RBinsonB/sharkhead-tx2-case/documentation/pictures/buttons_cad.png

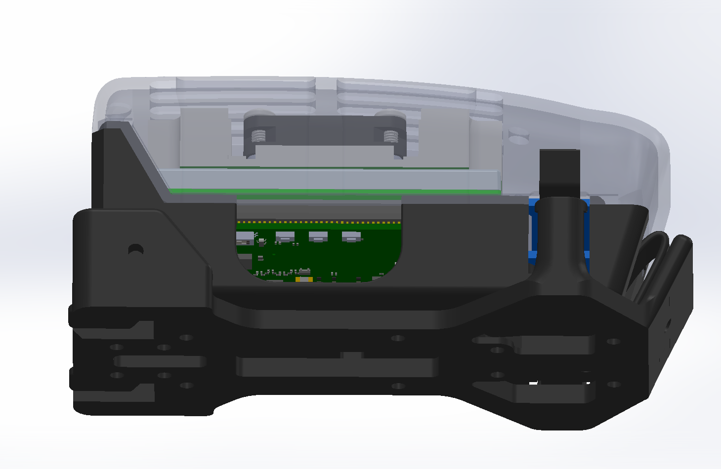
documentation/pictures/buttons_cad.png
