RBinsonB/sharkhead-tx2-case/documentation/pictures/gpio_cad.png

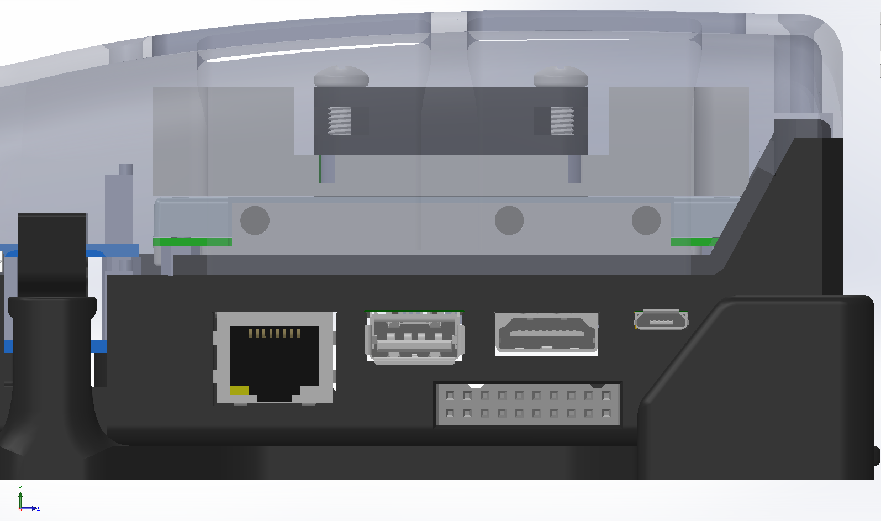
documentation/pictures/gpio_cad.png
