RBinsonB/sharkhead-tx2-case/documentation/pictures/gpio_cad_details.png

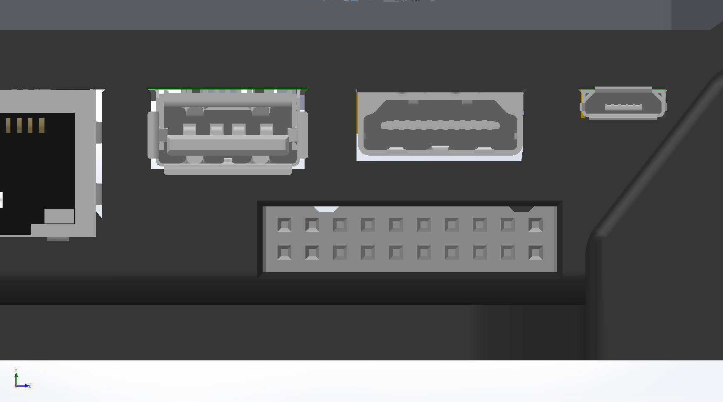
documentation/pictures/gpio_cad_details.png
