RBinsonB/sharkhead-tx2-case/documentation/pictures/rear_cad.png

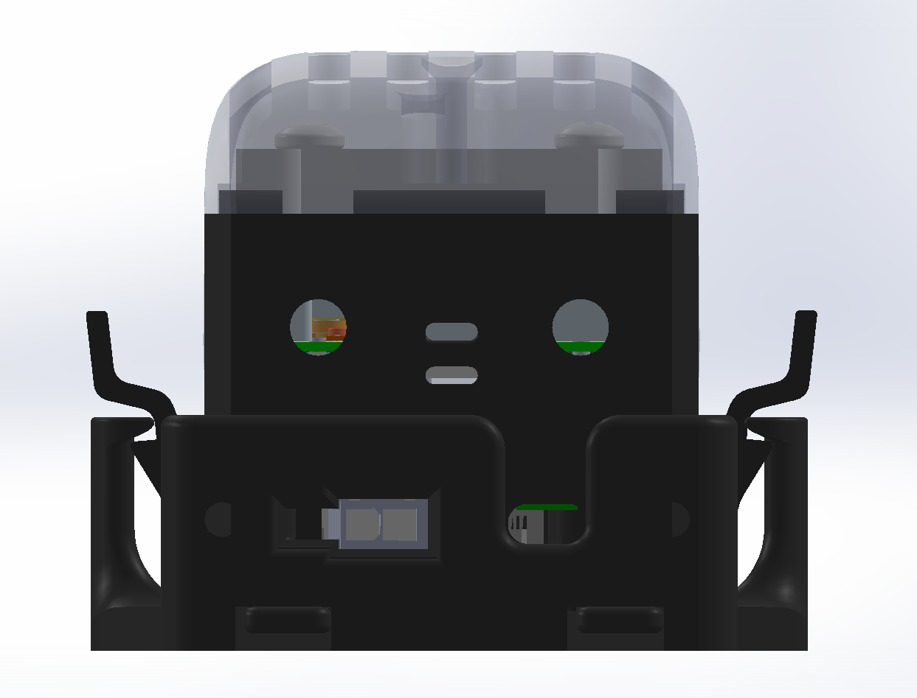
documentation/pictures/rear_cad.png
