RBinsonB/sharkhead-tx2-case/documentation/pictures/removing_1.jpg

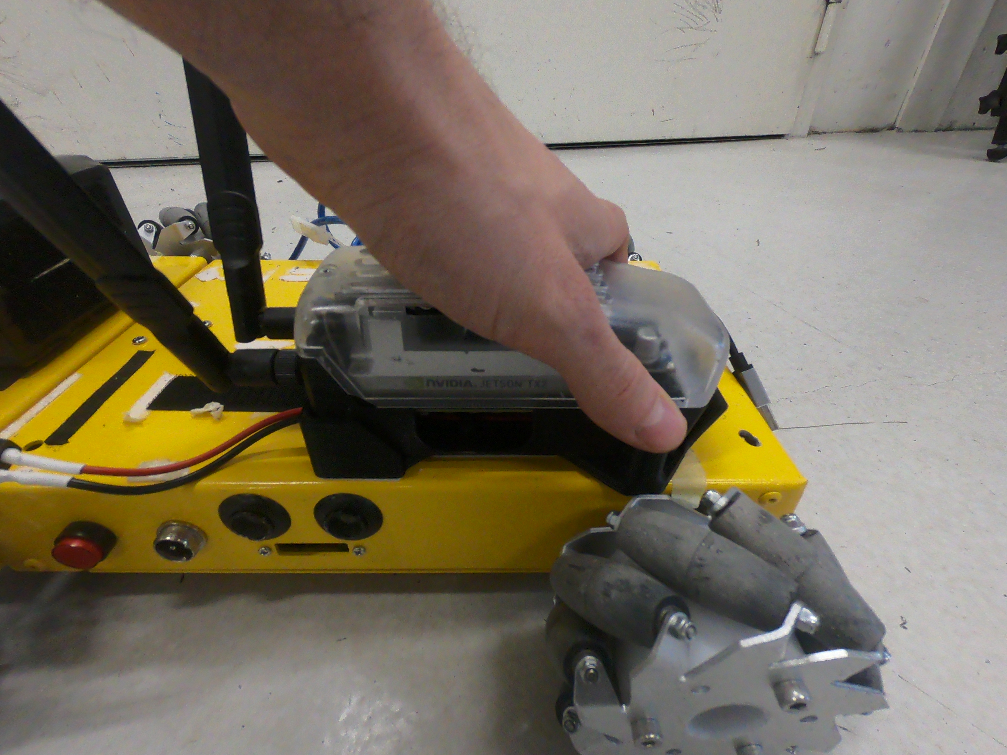
documentation/pictures/removing_1.jpg
