RBinsonB/sharkhead-tx2-case/documentation/pictures/render_1.png

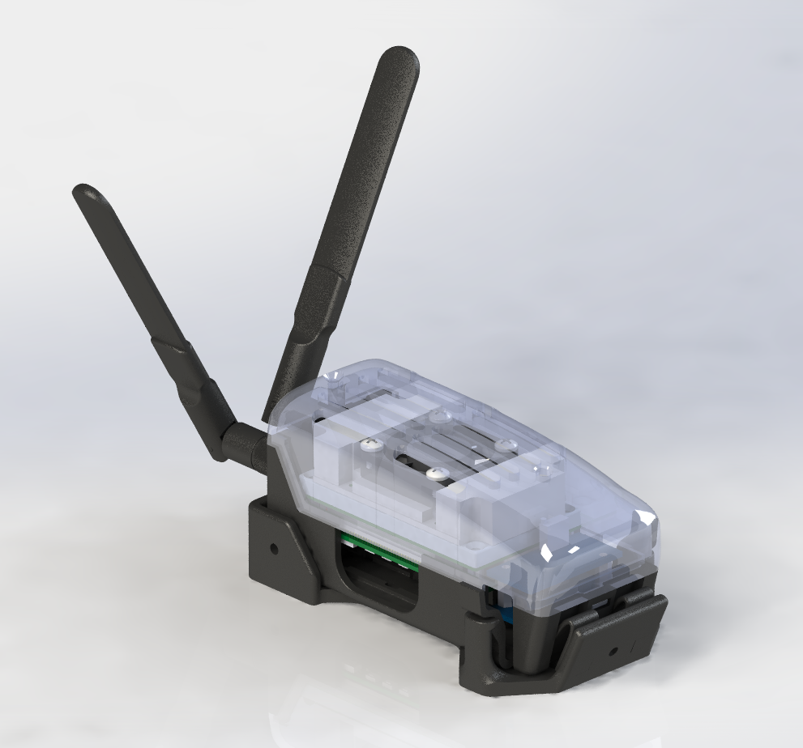
documentation/pictures/render_1.png
