RBinsonB/sharkhead-tx2-case/documentation/pictures/render_3.png

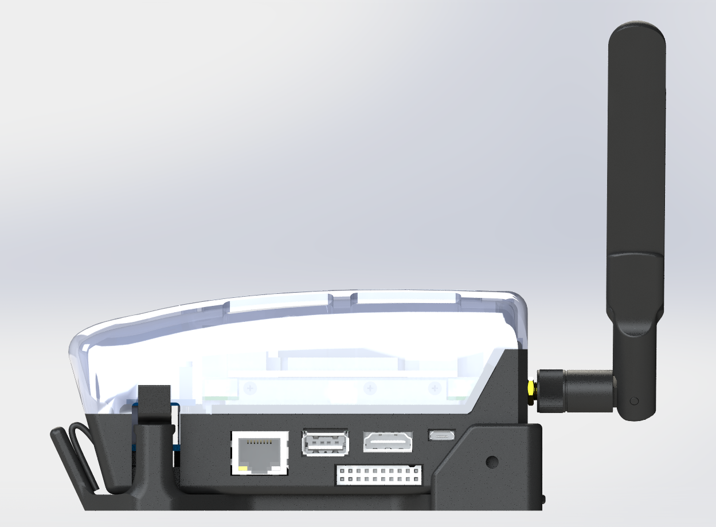
documentation/pictures/render_3.png
