RBinsonB/sharkhead-tx2-case/documentation/pictures/render_4.png

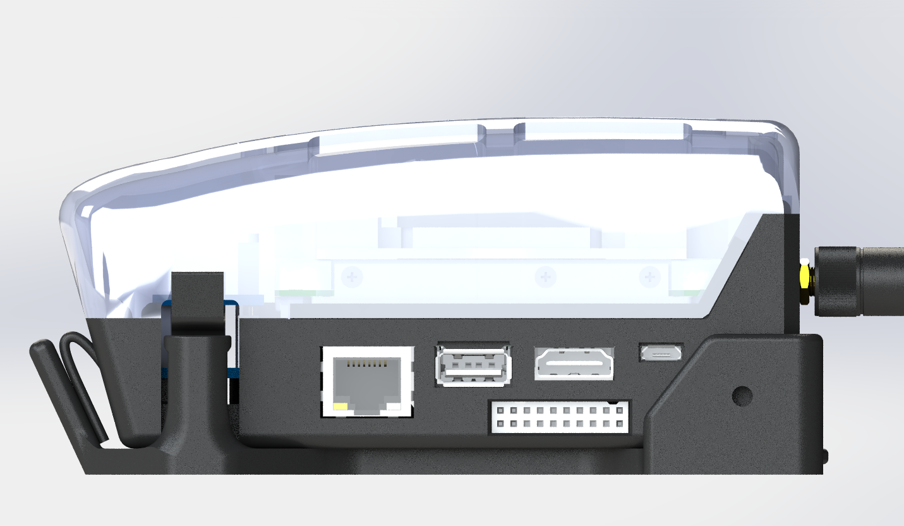
documentation/pictures/render_4.png
