RBinsonB/sharkhead-tx2-case/documentation/pictures/render_5.png

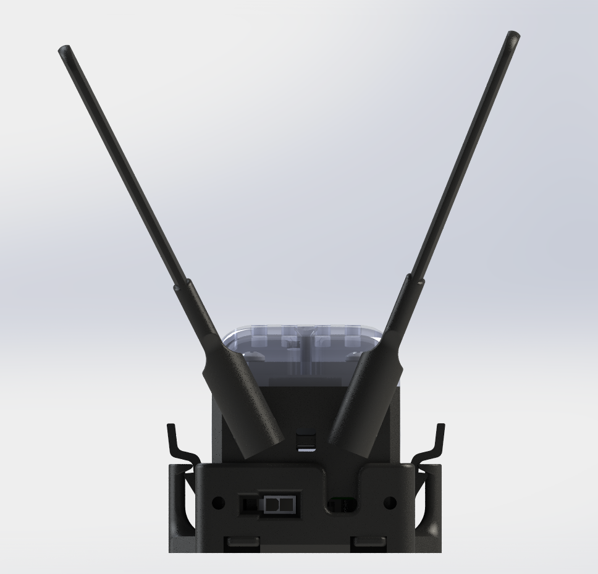
documentation/pictures/render_5.png
