RBinsonB/sharkhead-tx2-case/documentation/pictures/render_6.png

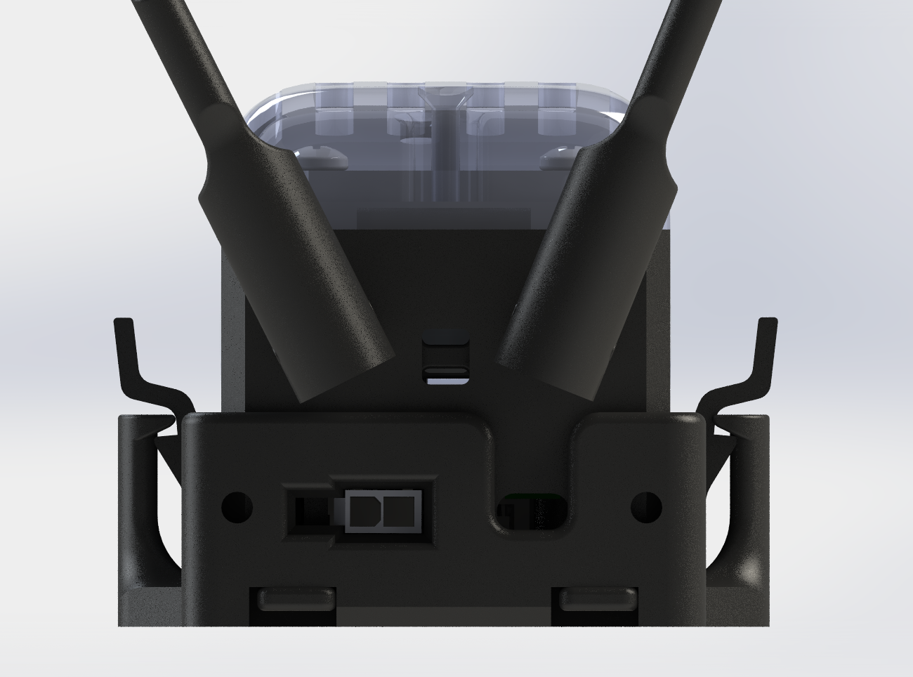
documentation/pictures/render_6.png
