RBinsonB/sharkhead-tx2-case/documentation/pictures/render_7.png

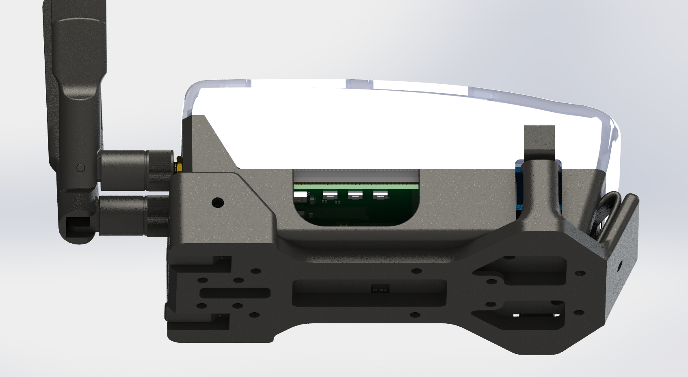
documentation/pictures/render_7.png
