RBinsonB/sharkhead-tx2-case/documentation/pictures/assembly/adjust_output_voltage.JPG

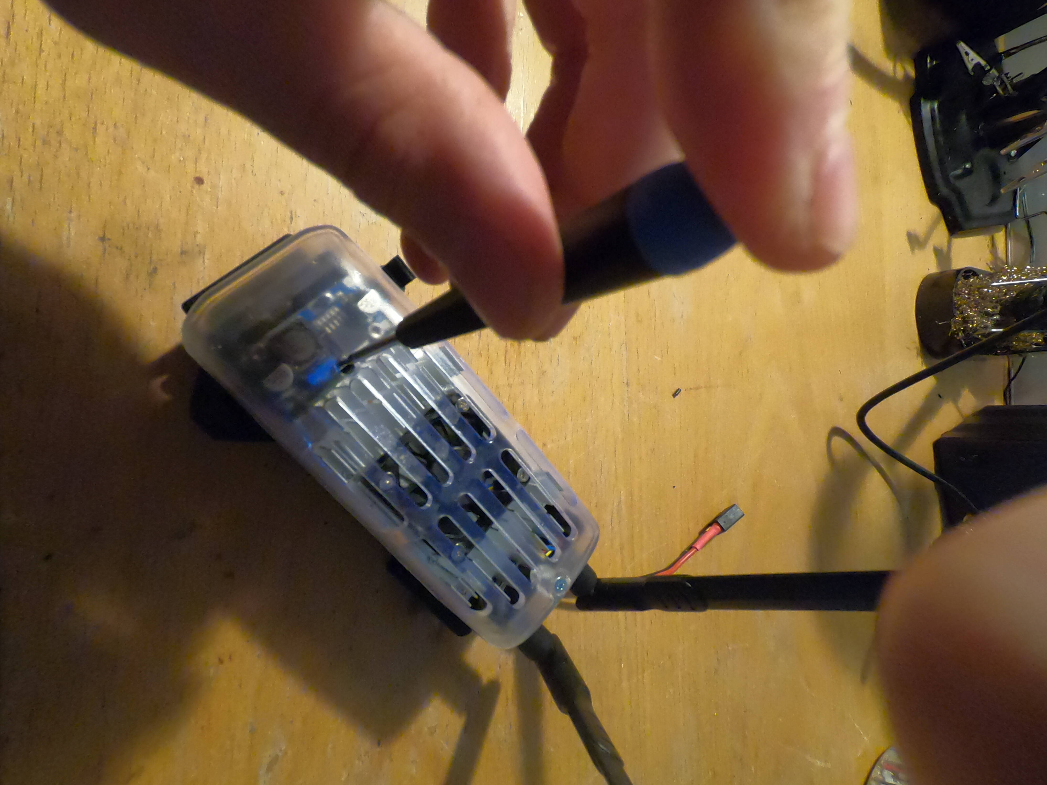
documentation/pictures/assembly/adjust_output_voltage.JPG
