RBinsonB/sharkhead-tx2-case/documentation/pictures/assembly/assembly14.JPG

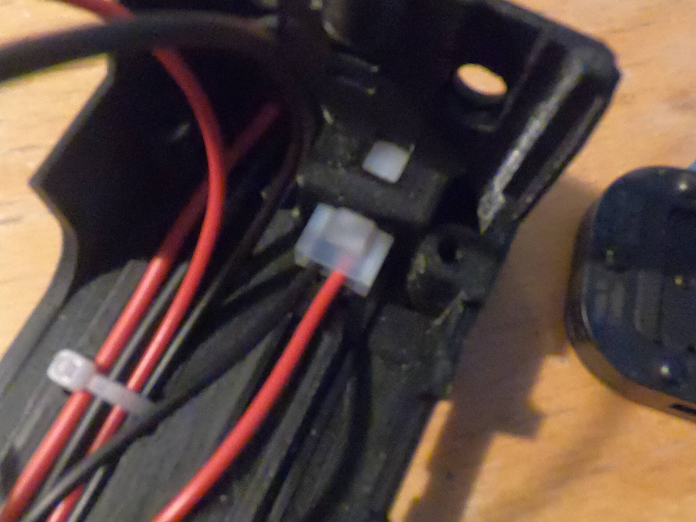
documentation/pictures/assembly/assembly14.JPG
