RBinsonB/sharkhead-tx2-case/documentation/pictures/assembly/assembly18.JPG

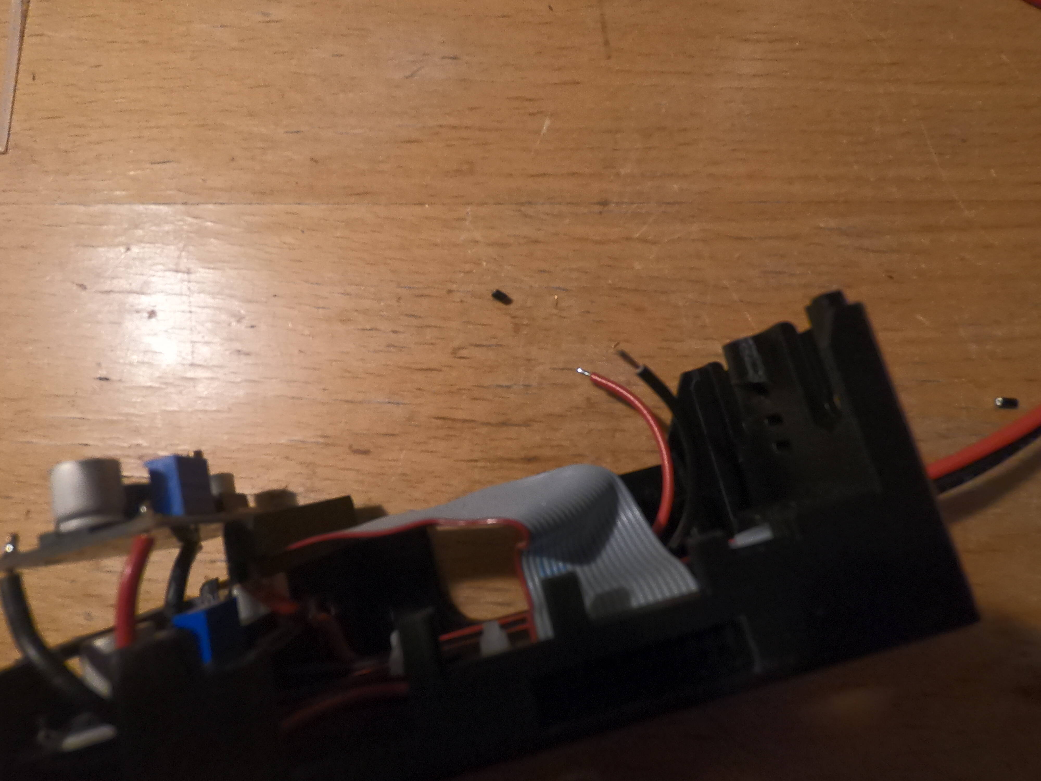
documentation/pictures/assembly/assembly18.JPG
