RBinsonB/sharkhead-tx2-case/documentation/pictures/assembly/assembly20.JPG

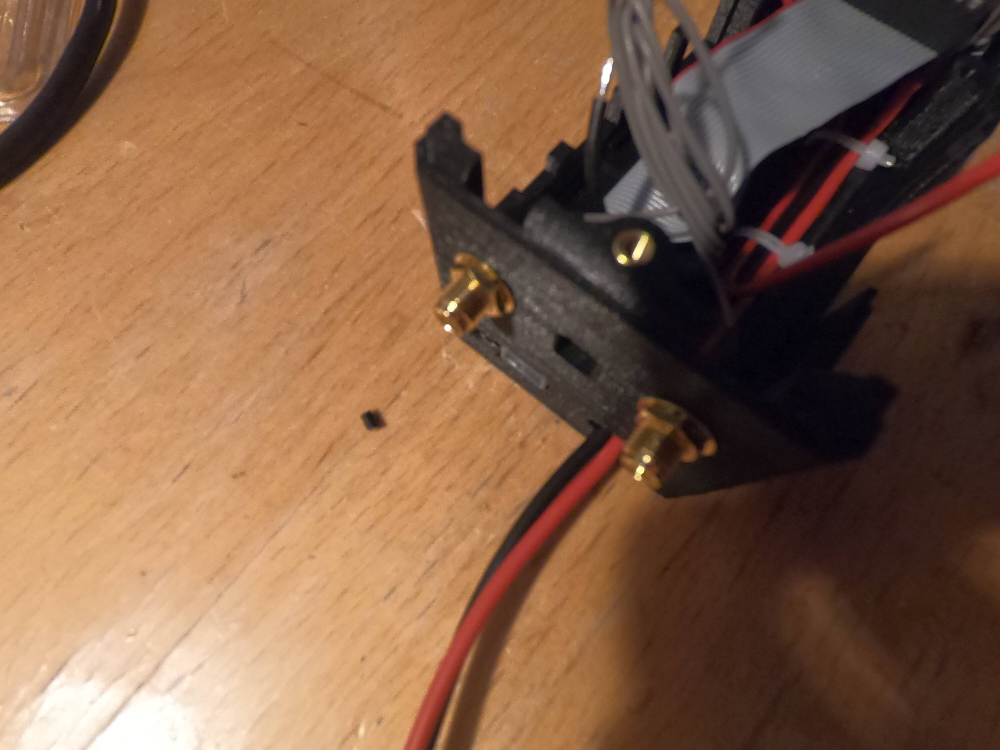
documentation/pictures/assembly/assembly20.JPG
