RBinsonB/sharkhead-tx2-case/documentation/pictures/assembly/assembly29.JPG

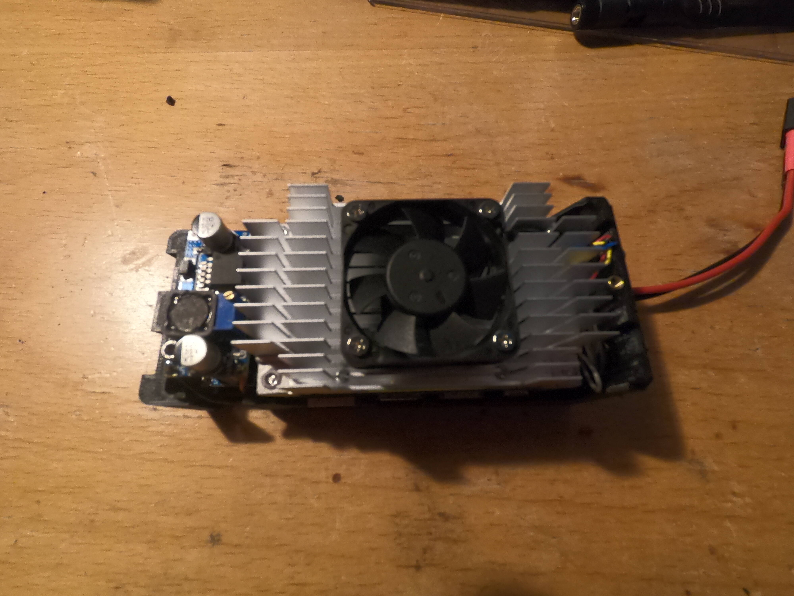
documentation/pictures/assembly/assembly29.JPG
