RBinsonB/sharkhead-tx2-case/documentation/pictures/assembly/assembly30.JPG

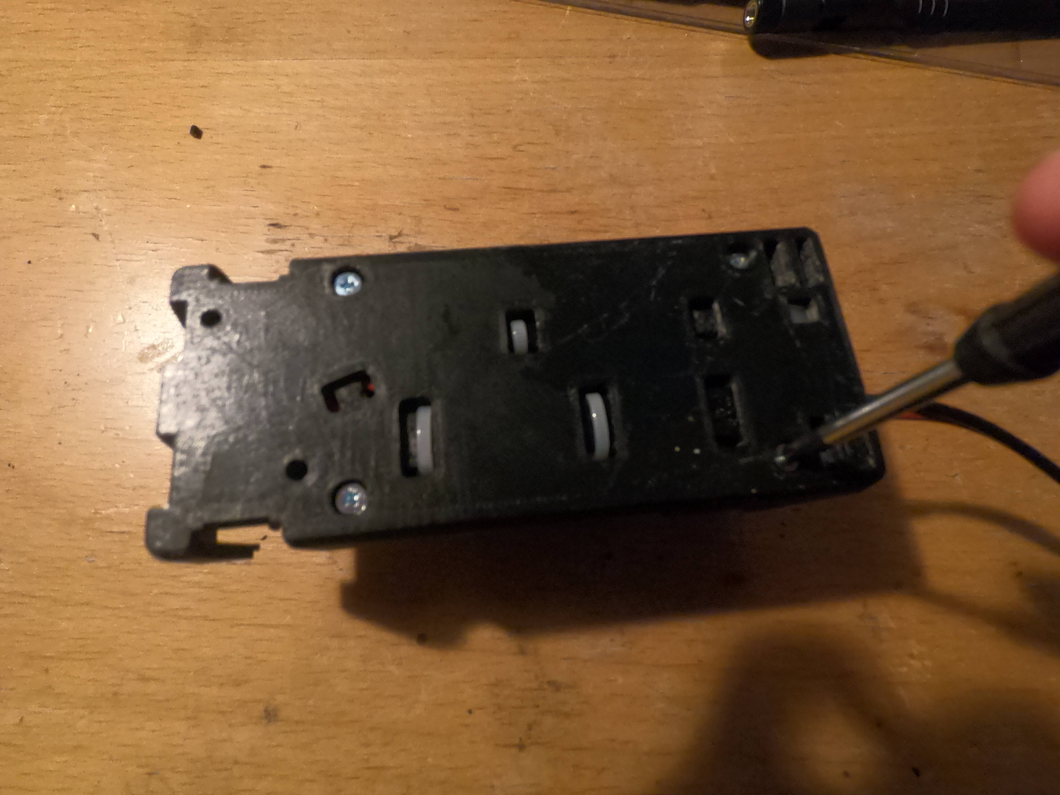
documentation/pictures/assembly/assembly30.JPG
