RBinsonB/sharkhead-tx2-case/documentation/pictures/installing_1.jpg

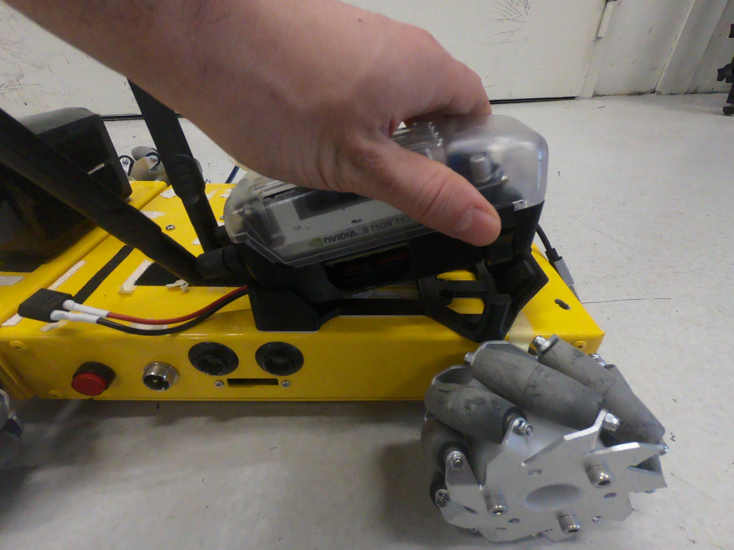
documentation/pictures/installing_1.jpg
